rmeuth01/Astro/Software/FrontEnd/es-theme-epicnoir-ARES/_art/controllers/lightgun.png

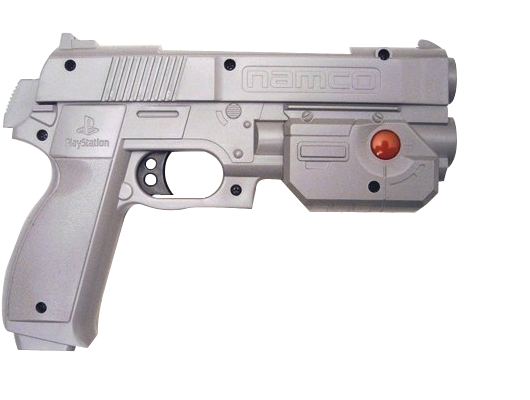
Software/FrontEnd/es-theme-epicnoir-ARES/_art/controllers/lightgun.png
