rmeuth01/Astro/Software/FrontEnd/es-theme-epicnoir-ARES/_art/controllers/3ds.png

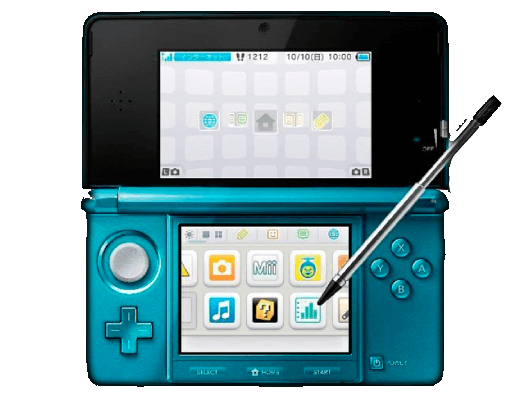
Software/FrontEnd/es-theme-epicnoir-ARES/_art/controllers/3ds.png
