rmeuth01/Astro/Software/FrontEnd/es-theme-epicnoir-ARES/_art/controllers/3do.png

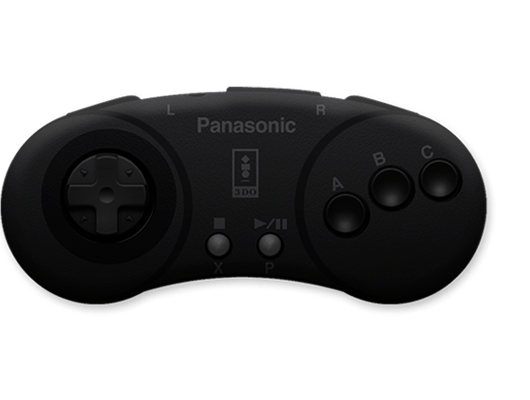
Software/FrontEnd/es-theme-epicnoir-ARES/_art/controllers/3do.png
