rmeuth01/Astro/Software/FrontEnd/es-theme-epicnoir-ARES/_art/controllers/action.png

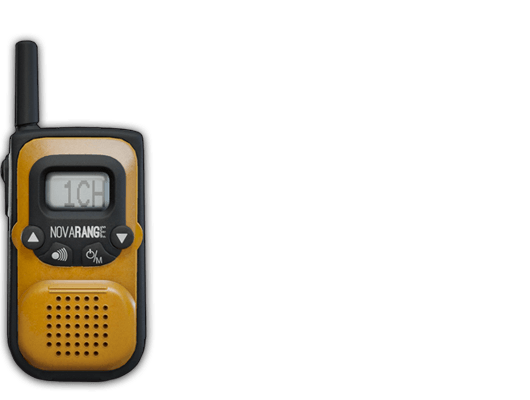
Software/FrontEnd/es-theme-epicnoir-ARES/_art/controllers/action.png
