rmeuth01/Astro/Software/FrontEnd/es-theme-epicnoir-ARES/_art/controllers/adventure.png

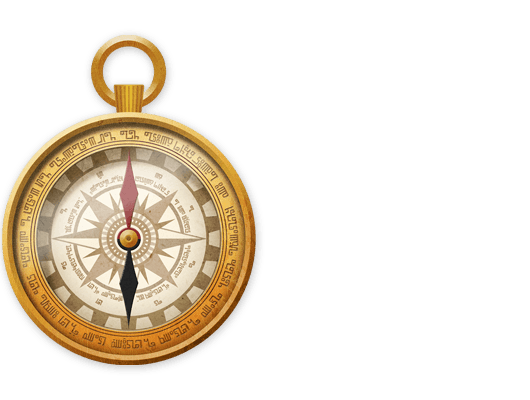
Software/FrontEnd/es-theme-epicnoir-ARES/_art/controllers/adventure.png
