rmeuth01/Astro/Software/FrontEnd/es-theme-epicnoir-ARES/_art/controllers/amiga1200.png

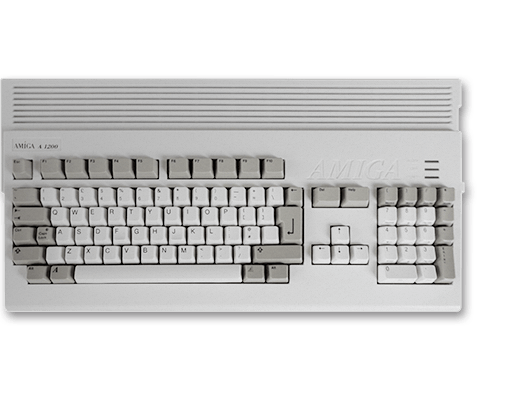
Software/FrontEnd/es-theme-epicnoir-ARES/_art/controllers/amiga1200.png
