rmeuth01/Astro/Software/FrontEnd/es-theme-epicnoir-ARES/_art/controllers/amstradcpc.png

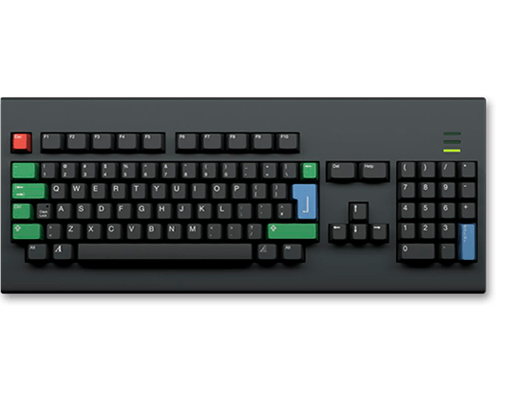
Software/FrontEnd/es-theme-epicnoir-ARES/_art/controllers/amstradcpc.png
