rmeuth01/Astro/Software/FrontEnd/es-theme-epicnoir-ARES/_art/controllers/arcade.png

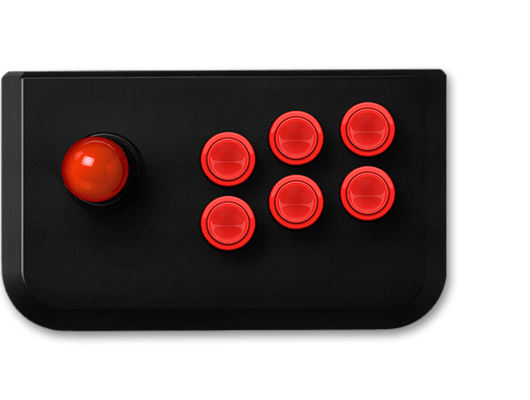
Software/FrontEnd/es-theme-epicnoir-ARES/_art/controllers/arcade.png
