rmeuth01/Astro/Software/FrontEnd/es-theme-epicnoir-ARES/_art/controllers/atari2600.png

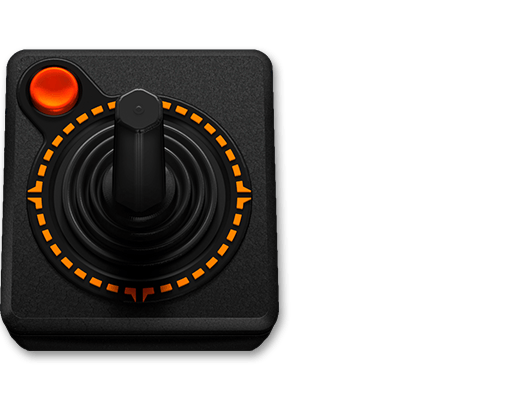
Software/FrontEnd/es-theme-epicnoir-ARES/_art/controllers/atari2600.png
