rmeuth01/Astro/Software/FrontEnd/es-theme-epicnoir-ARES/_art/controllers/atari5200.png

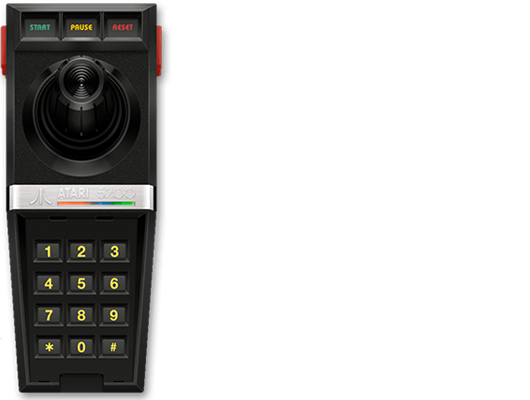
Software/FrontEnd/es-theme-epicnoir-ARES/_art/controllers/atari5200.png
