rmeuth01/Astro/Software/FrontEnd/es-theme-epicnoir-ARES/_art/controllers/atari7800.png

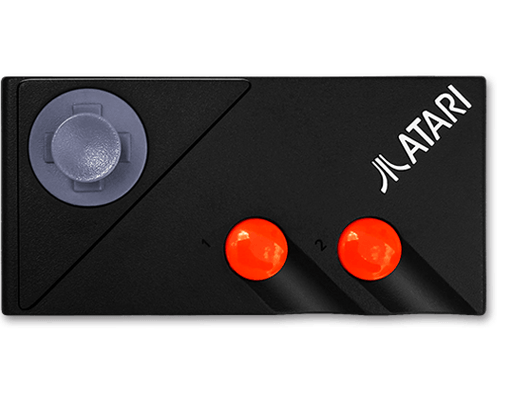
Software/FrontEnd/es-theme-epicnoir-ARES/_art/controllers/atari7800.png
