rmeuth01/Astro/Software/FrontEnd/es-theme-epicnoir-ARES/_art/controllers/atarijaguar.png

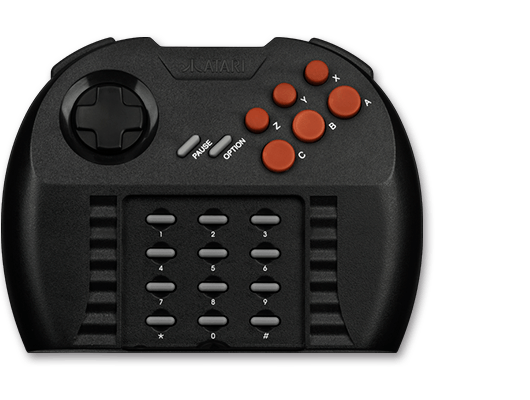
Software/FrontEnd/es-theme-epicnoir-ARES/_art/controllers/atarijaguar.png
