rmeuth01/Astro/Software/FrontEnd/es-theme-epicnoir-ARES/_art/controllers/atarilynx.png

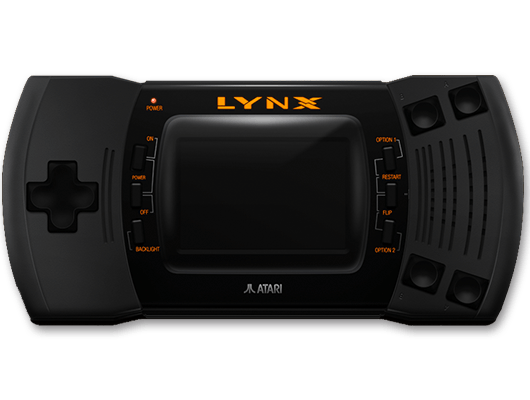
Software/FrontEnd/es-theme-epicnoir-ARES/_art/controllers/atarilynx.png
