rmeuth01/Astro/Software/FrontEnd/es-theme-epicnoir-ARES/_art/controllers/atarist.png

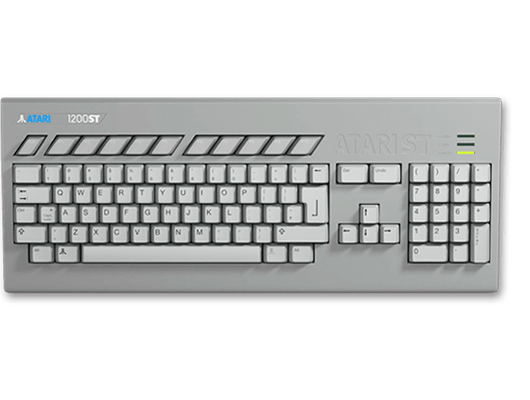
Software/FrontEnd/es-theme-epicnoir-ARES/_art/controllers/atarist.png
