rmeuth01/Astro/Software/FrontEnd/es-theme-epicnoir-ARES/_art/controllers/auto-allgames.png

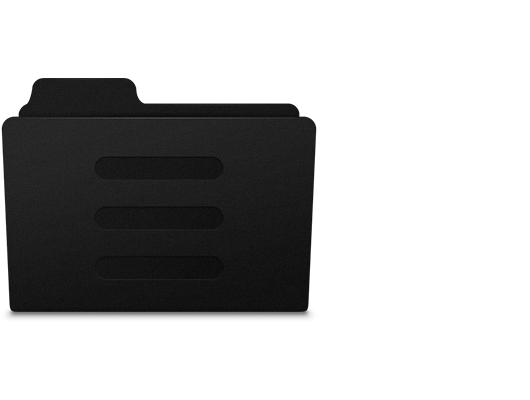
Software/FrontEnd/es-theme-epicnoir-ARES/_art/controllers/auto-allgames.png
