rmeuth01/Astro/Software/FrontEnd/es-theme-epicnoir-ARES/_art/controllers/btmups.png

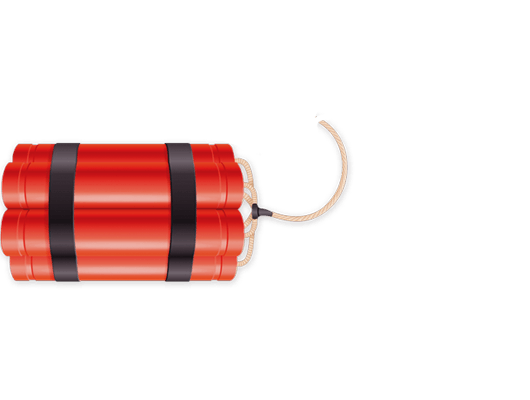
Software/FrontEnd/es-theme-epicnoir-ARES/_art/controllers/btmups.png
