rmeuth01/Astro/Software/FrontEnd/es-theme-epicnoir-ARES/_art/controllers/c16.png

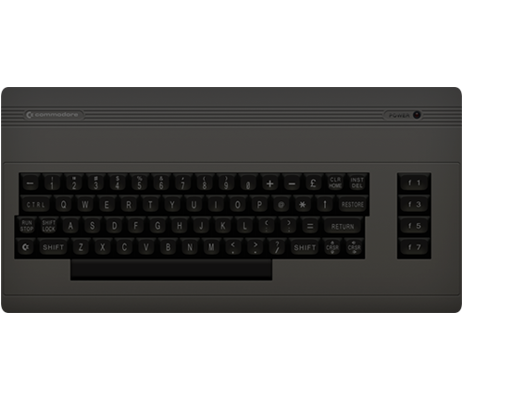
Software/FrontEnd/es-theme-epicnoir-ARES/_art/controllers/c16.png
