rmeuth01/Astro/Software/FrontEnd/es-theme-epicnoir-ARES/_art/controllers/coco.png

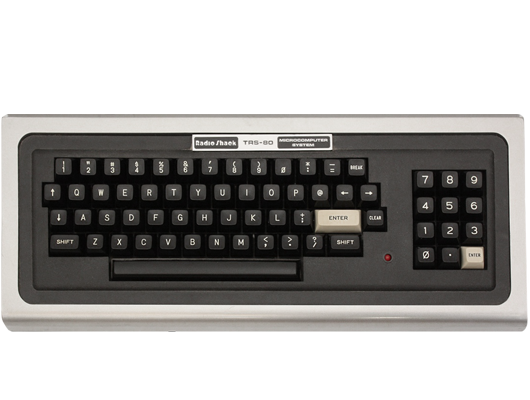
Software/FrontEnd/es-theme-epicnoir-ARES/_art/controllers/coco.png
