rmeuth01/Astro/Software/FrontEnd/es-theme-epicnoir-ARES/_art/controllers/colecovision.png

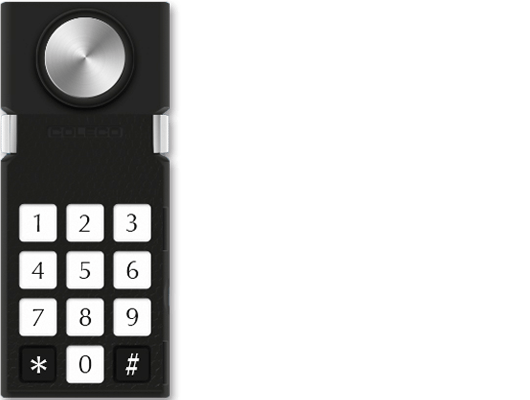
Software/FrontEnd/es-theme-epicnoir-ARES/_art/controllers/colecovision.png
