rmeuth01/Astro/Software/FrontEnd/es-theme-epicnoir-ARES/_art/controllers/dreamcast.png

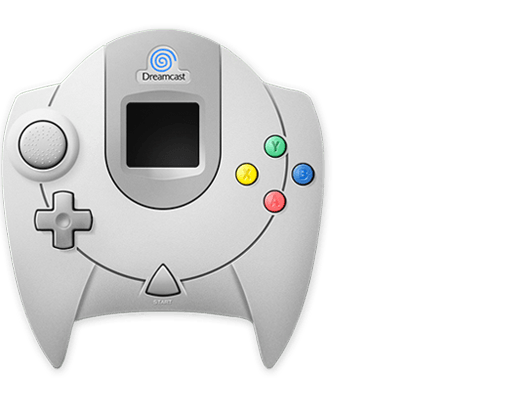
Software/FrontEnd/es-theme-epicnoir-ARES/_art/controllers/dreamcast.png
