rmeuth01/Astro/Software/FrontEnd/es-theme-epicnoir-ARES/_art/controllers/famicom.png

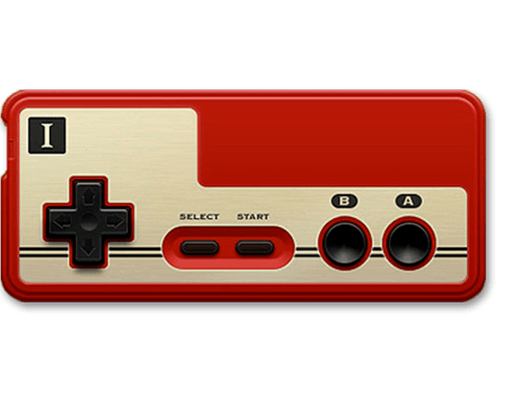
Software/FrontEnd/es-theme-epicnoir-ARES/_art/controllers/famicom.png
