rmeuth01/Astro/Software/FrontEnd/es-theme-epicnoir-ARES/_art/controllers/fighting.png

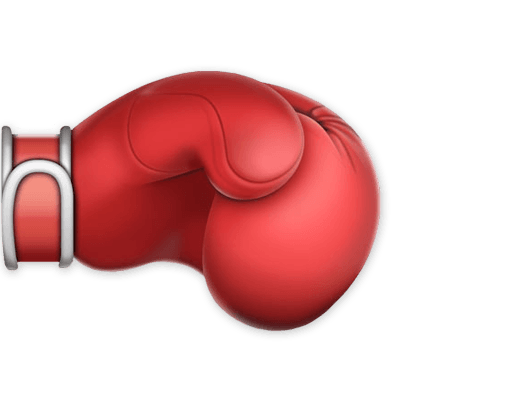
Software/FrontEnd/es-theme-epicnoir-ARES/_art/controllers/fighting.png
