rmeuth01/Astro/Software/FrontEnd/es-theme-epicnoir-ARES/_art/controllers/gameandwatch.png

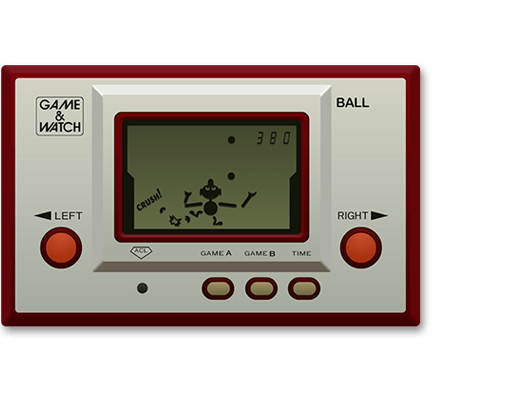
Software/FrontEnd/es-theme-epicnoir-ARES/_art/controllers/gameandwatch.png
