rmeuth01/Astro/Software/FrontEnd/es-theme-epicnoir-ARES/_art/controllers/gamegear.png

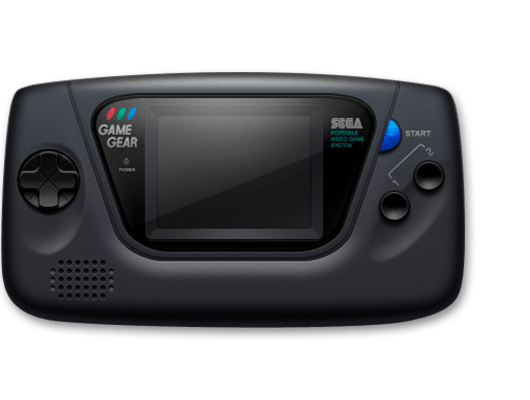
Software/FrontEnd/es-theme-epicnoir-ARES/_art/controllers/gamegear.png
