rmeuth01/Astro/Software/FrontEnd/es-theme-epicnoir-ARES/_art/controllers/gb.png

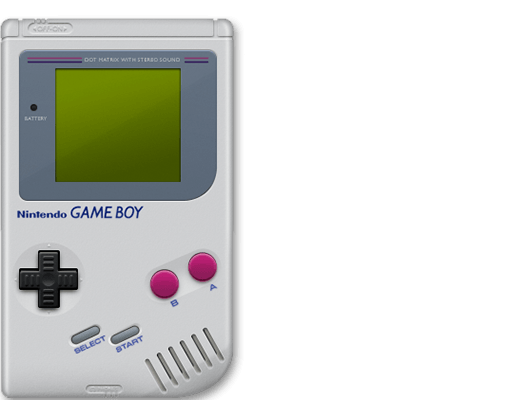
Software/FrontEnd/es-theme-epicnoir-ARES/_art/controllers/gb.png
