rmeuth01/Astro/Software/FrontEnd/es-theme-epicnoir-ARES/_art/controllers/gba.png

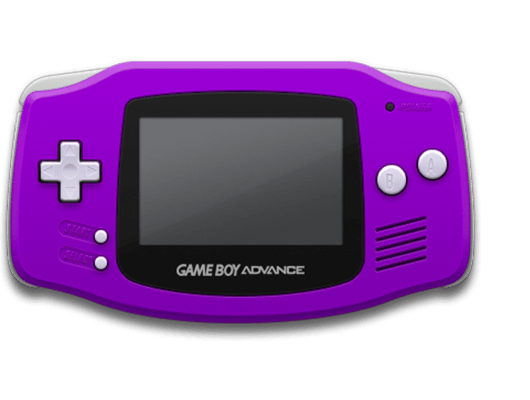
Software/FrontEnd/es-theme-epicnoir-ARES/_art/controllers/gba.png
