rmeuth01/Astro/Software/FrontEnd/es-theme-epicnoir-ARES/_art/controllers/gbc.png

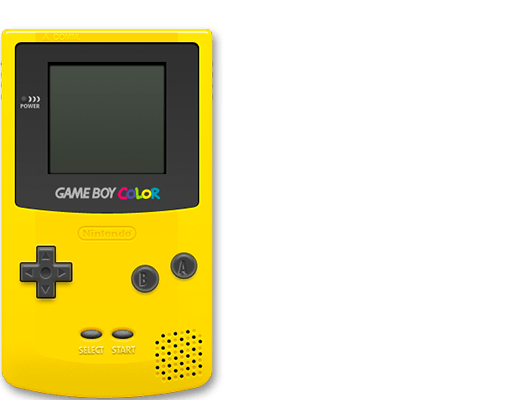
Software/FrontEnd/es-theme-epicnoir-ARES/_art/controllers/gbc.png
