rmeuth01/Astro/Software/FrontEnd/es-theme-epicnoir-ARES/_art/controllers/gc.png

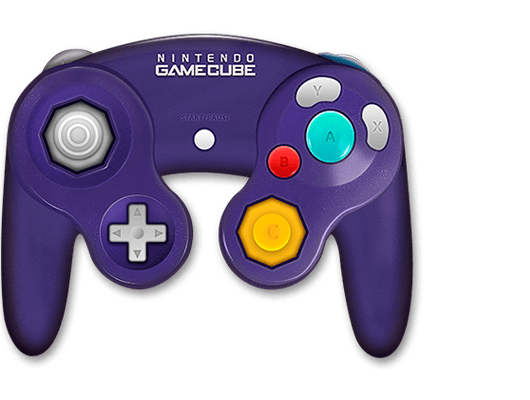
Software/FrontEnd/es-theme-epicnoir-ARES/_art/controllers/gc.png
