rmeuth01/Astro/Software/FrontEnd/es-theme-epicnoir-ARES/_art/controllers/genesis.png

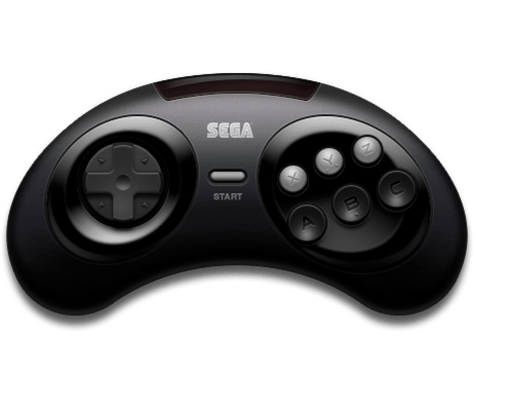
Software/FrontEnd/es-theme-epicnoir-ARES/_art/controllers/genesis.png
