rmeuth01/Astro/Software/FrontEnd/es-theme-epicnoir-ARES/_art/controllers/intellivision.png

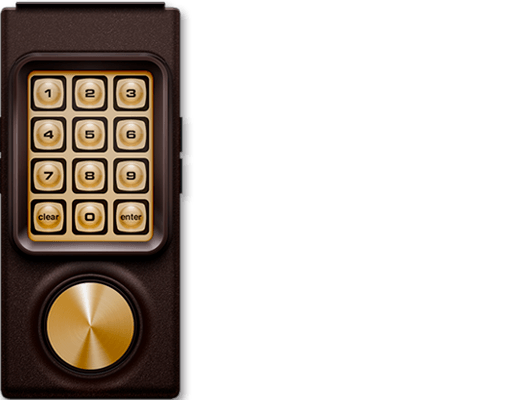
Software/FrontEnd/es-theme-epicnoir-ARES/_art/controllers/intellivision.png
