rmeuth01/Astro/Software/FrontEnd/es-theme-epicnoir-ARES/_art/controllers/kids.png

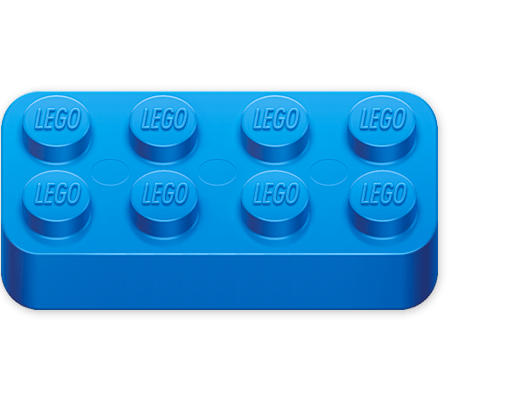
Software/FrontEnd/es-theme-epicnoir-ARES/_art/controllers/kids.png
