rmeuth01/Astro/Software/FrontEnd/es-theme-epicnoir-ARES/_art/controllers/kodi.png

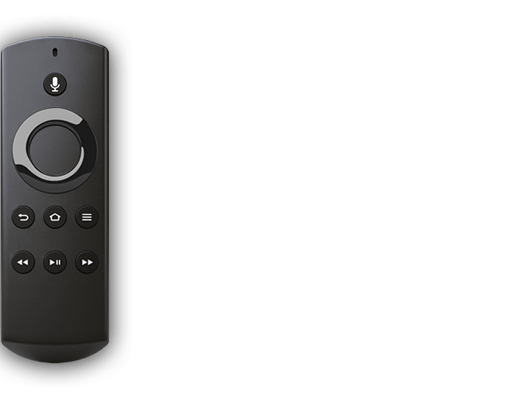
Software/FrontEnd/es-theme-epicnoir-ARES/_art/controllers/kodi.png
