rmeuth01/Astro/Software/FrontEnd/es-theme-epicnoir-ARES/_art/controllers/mastersystem.png

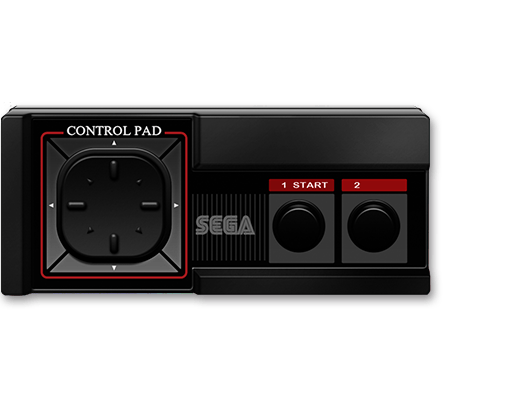
Software/FrontEnd/es-theme-epicnoir-ARES/_art/controllers/mastersystem.png
