rmeuth01/Astro/Software/FrontEnd/es-theme-epicnoir-ARES/_art/controllers/msx2.png

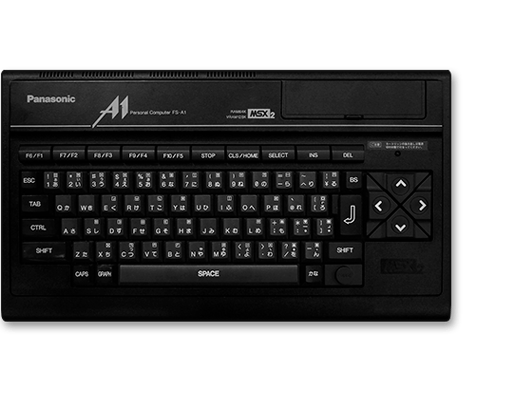
Software/FrontEnd/es-theme-epicnoir-ARES/_art/controllers/msx2.png
