rmeuth01/Astro/Software/FrontEnd/es-theme-epicnoir-ARES/_art/controllers/msx-fs8.png

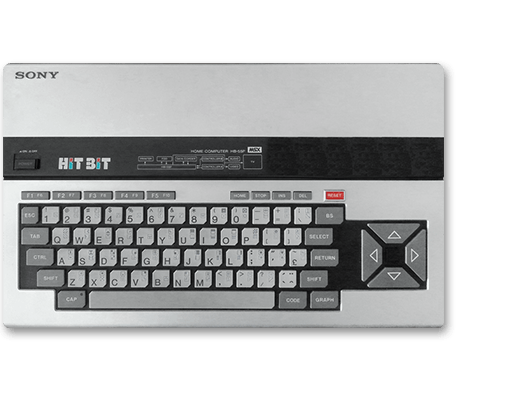
Software/FrontEnd/es-theme-epicnoir-ARES/_art/controllers/msx-fs8.png
