rmeuth01/Astro/Software/FrontEnd/es-theme-epicnoir-ARES/_art/controllers/n64.png

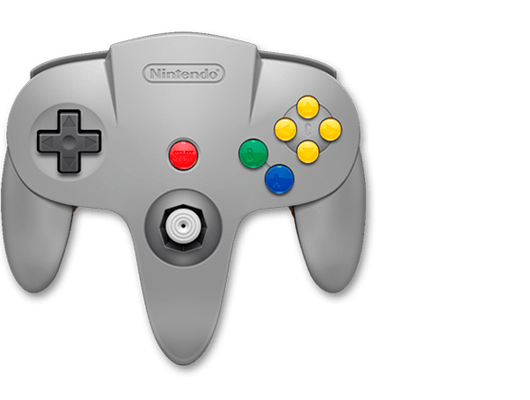
Software/FrontEnd/es-theme-epicnoir-ARES/_art/controllers/n64.png
