rmeuth01/Astro/Software/FrontEnd/es-theme-epicnoir-ARES/_art/controllers/nds.png

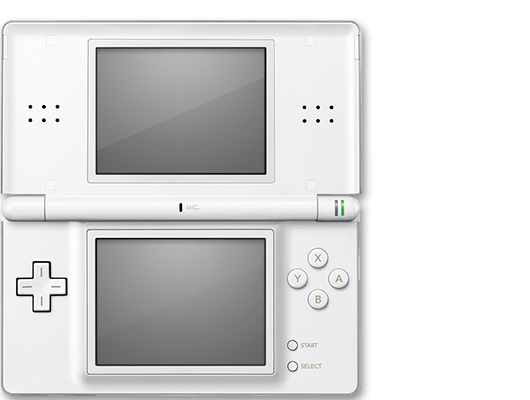
Software/FrontEnd/es-theme-epicnoir-ARES/_art/controllers/nds.png
