rmeuth01/Astro/Software/FrontEnd/es-theme-epicnoir-ARES/_art/controllers/neogeo.png

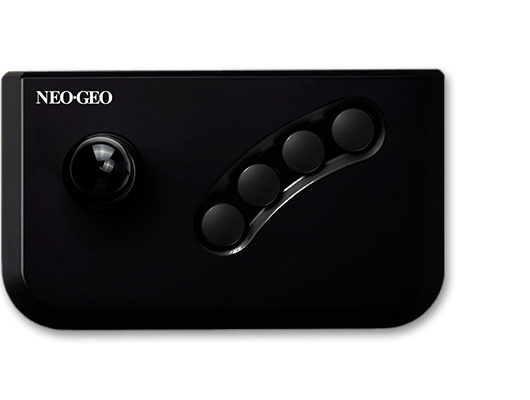
Software/FrontEnd/es-theme-epicnoir-ARES/_art/controllers/neogeo.png
