rmeuth01/Astro/Software/FrontEnd/es-theme-epicnoir-ARES/_art/controllers/neogeocd.png

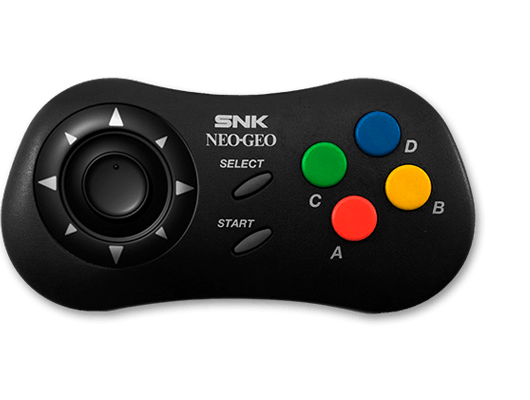
Software/FrontEnd/es-theme-epicnoir-ARES/_art/controllers/neogeocd.png
