rmeuth01/Astro/Software/FrontEnd/es-theme-epicnoir-ARES/_art/controllers/nes.png

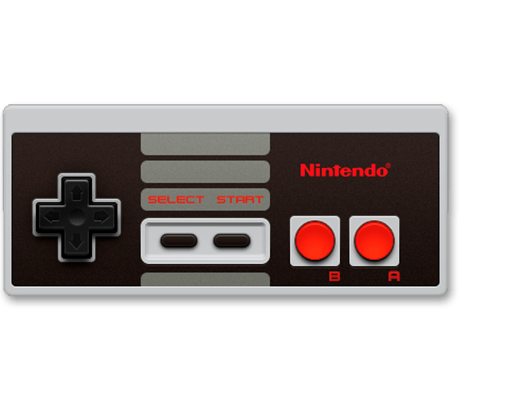
Software/FrontEnd/es-theme-epicnoir-ARES/_art/controllers/nes.png
