rmeuth01/Astro/Software/FrontEnd/es-theme-epicnoir-ARES/_art/controllers/ngp.png

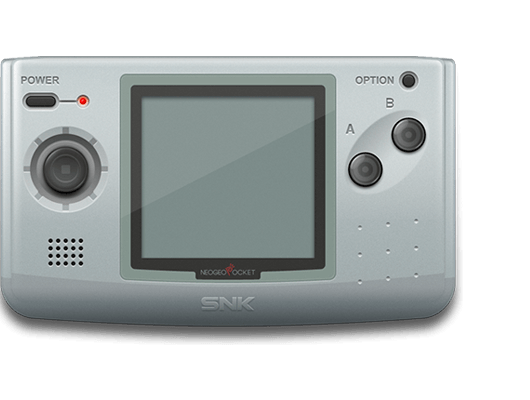
Software/FrontEnd/es-theme-epicnoir-ARES/_art/controllers/ngp.png
