rmeuth01/Astro/Software/FrontEnd/es-theme-epicnoir-ARES/_art/controllers/pc98.png

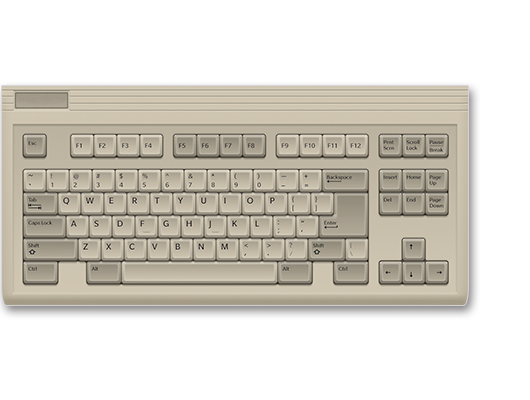
Software/FrontEnd/es-theme-epicnoir-ARES/_art/controllers/pc98.png
