rmeuth01/Astro/Software/FrontEnd/es-theme-epicnoir-ARES/_art/controllers/pce-cd.png

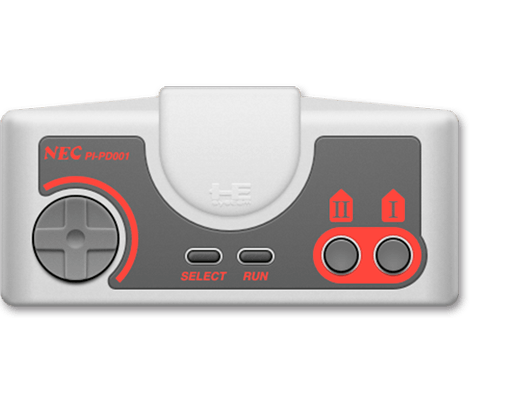
Software/FrontEnd/es-theme-epicnoir-ARES/_art/controllers/pce-cd.png
