rmeuth01/Astro/Software/FrontEnd/es-theme-epicnoir-ARES/_art/controllers/platformers.png

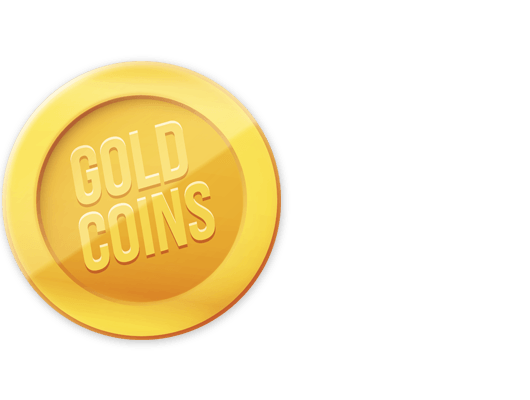
Software/FrontEnd/es-theme-epicnoir-ARES/_art/controllers/platformers.png
