rmeuth01/Astro/Software/FrontEnd/es-theme-epicnoir-ARES/_art/controllers/ports.png

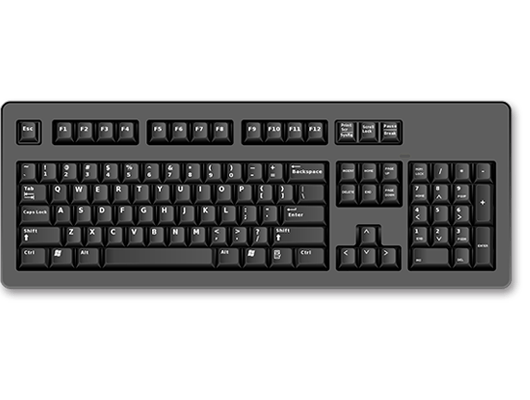
Software/FrontEnd/es-theme-epicnoir-ARES/_art/controllers/ports.png
