rmeuth01/Astro/Software/FrontEnd/es-theme-epicnoir-ARES/_art/controllers/power.png

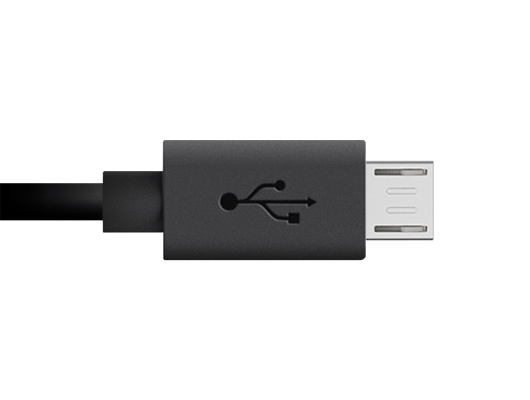
Software/FrontEnd/es-theme-epicnoir-ARES/_art/controllers/power.png
