rmeuth01/Astro/Software/FrontEnd/es-theme-epicnoir-ARES/_art/controllers/ps2.png

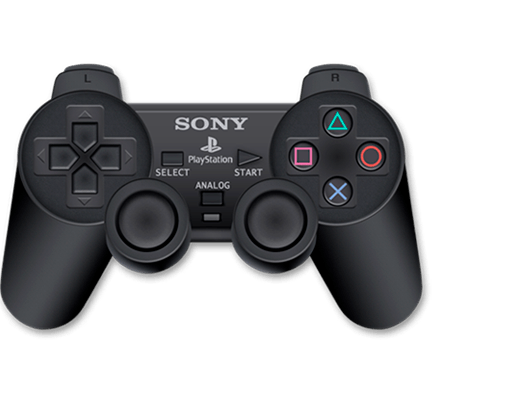
Software/FrontEnd/es-theme-epicnoir-ARES/_art/controllers/ps2.png
