rmeuth01/Astro/Software/FrontEnd/es-theme-epicnoir-ARES/_art/controllers/ps3.png

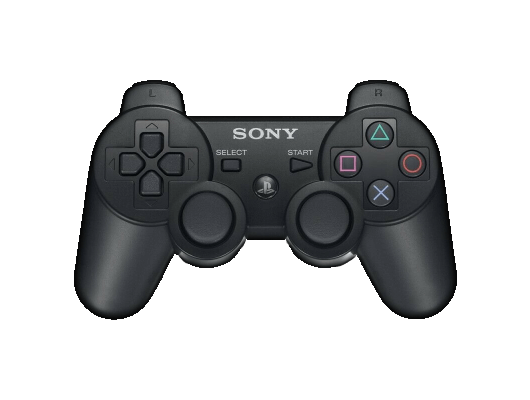
Software/FrontEnd/es-theme-epicnoir-ARES/_art/controllers/ps3.png
