rmeuth01/Astro/Software/FrontEnd/es-theme-epicnoir-ARES/_art/controllers/psp.png

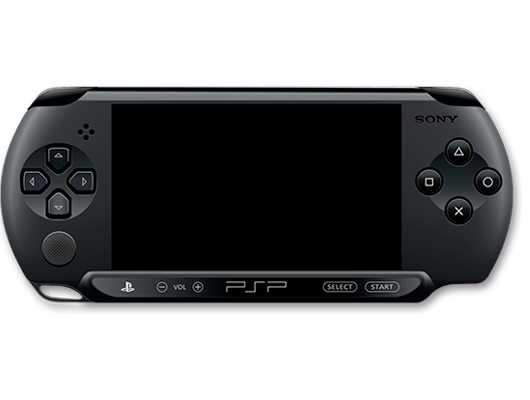
Software/FrontEnd/es-theme-epicnoir-ARES/_art/controllers/psp.png
