rmeuth01/Astro/Software/FrontEnd/es-theme-epicnoir-ARES/_art/controllers/psx.png

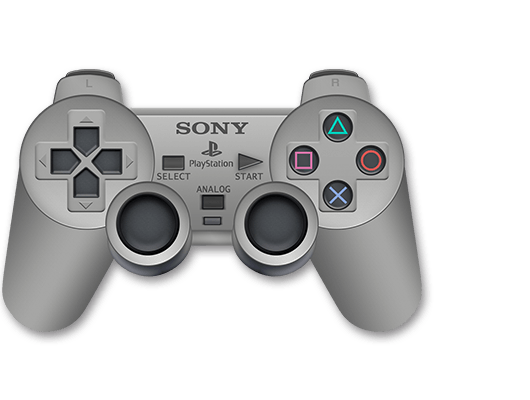
Software/FrontEnd/es-theme-epicnoir-ARES/_art/controllers/psx.png
