rmeuth01/Astro/Software/FrontEnd/es-theme-epicnoir-ARES/_art/controllers/puzzle.png

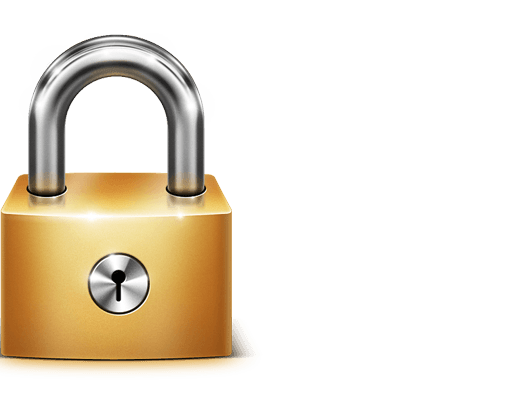
Software/FrontEnd/es-theme-epicnoir-ARES/_art/controllers/puzzle.png
