rmeuth01/Astro/Software/FrontEnd/es-theme-epicnoir-ARES/_art/controllers/racing.png

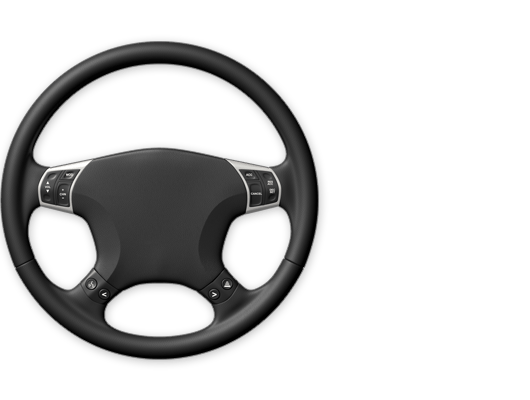
Software/FrontEnd/es-theme-epicnoir-ARES/_art/controllers/racing.png
