rmeuth01/Astro/Software/FrontEnd/es-theme-epicnoir-ARES/_art/controllers/residualvm.png

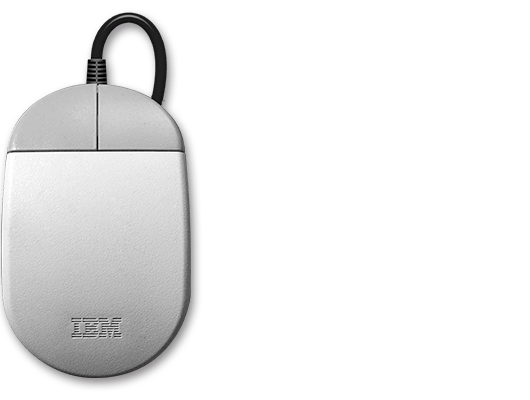
Software/FrontEnd/es-theme-epicnoir-ARES/_art/controllers/residualvm.png
