rmeuth01/Astro/Software/FrontEnd/es-theme-epicnoir-ARES/_art/controllers/retroarena.png

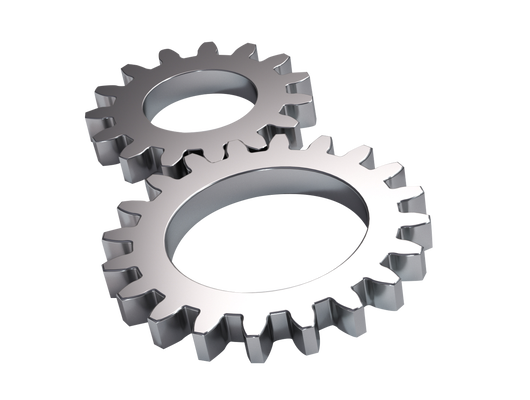
Software/FrontEnd/es-theme-epicnoir-ARES/_art/controllers/retroarena.png
