rmeuth01/Astro/Software/FrontEnd/es-theme-epicnoir-ARES/_art/controllers/retropie.png

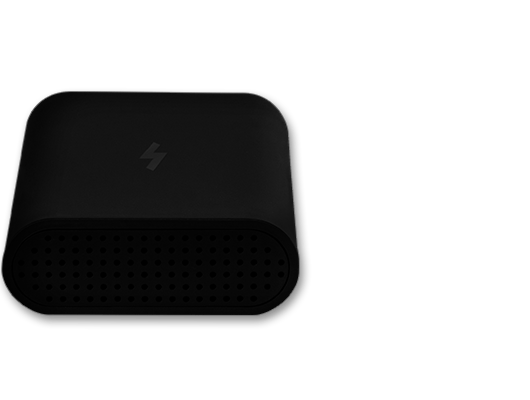
Software/FrontEnd/es-theme-epicnoir-ARES/_art/controllers/retropie.png
