rmeuth01/Astro/Software/FrontEnd/es-theme-epicnoir-ARES/_art/controllers/saturn.png

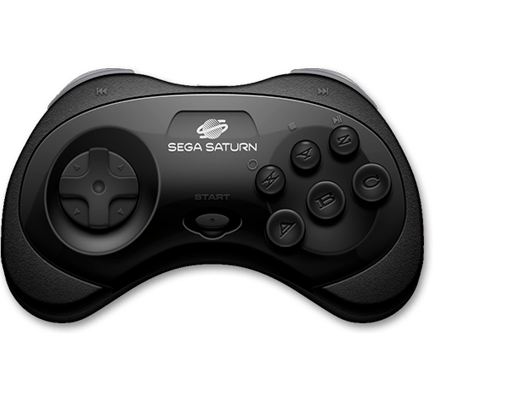
Software/FrontEnd/es-theme-epicnoir-ARES/_art/controllers/saturn.png
