rmeuth01/Astro/Software/FrontEnd/es-theme-epicnoir-ARES/_art/controllers/sfc.png

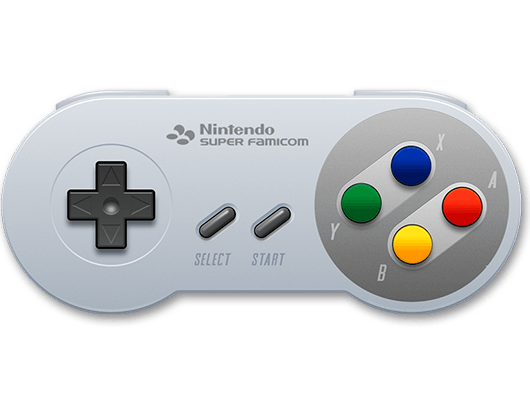
Software/FrontEnd/es-theme-epicnoir-ARES/_art/controllers/sfc.png
