rmeuth01/Astro/Software/FrontEnd/es-theme-epicnoir-ARES/_art/controllers/shmups.png

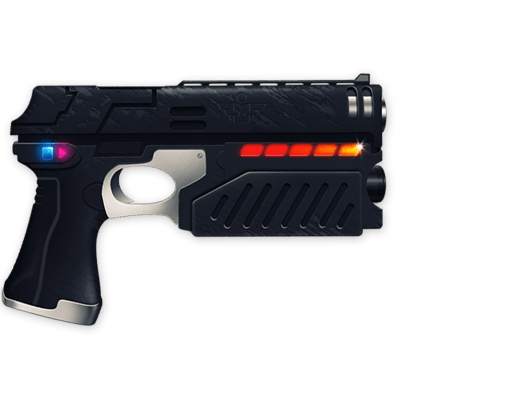
Software/FrontEnd/es-theme-epicnoir-ARES/_art/controllers/shmups.png
