rmeuth01/Astro/Software/FrontEnd/es-theme-epicnoir-ARES/_art/controllers/sports.png

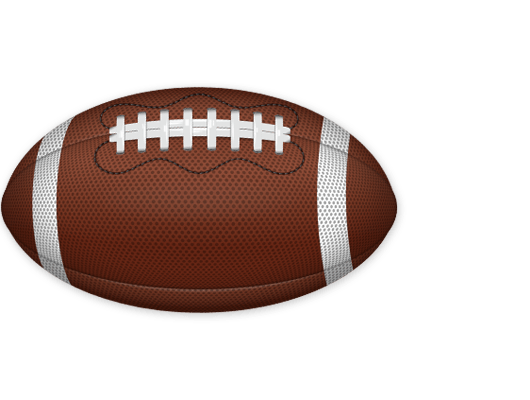
Software/FrontEnd/es-theme-epicnoir-ARES/_art/controllers/sports.png
