rmeuth01/Astro/Software/FrontEnd/es-theme-epicnoir-ARES/_art/controllers/steam.png

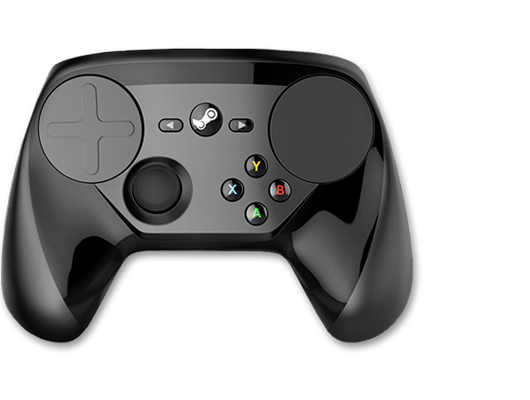
Software/FrontEnd/es-theme-epicnoir-ARES/_art/controllers/steam.png
