rmeuth01/Astro/Software/FrontEnd/es-theme-epicnoir-ARES/_art/controllers/strategy.png

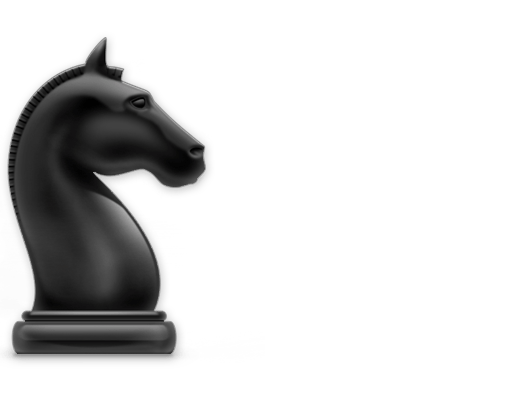
Software/FrontEnd/es-theme-epicnoir-ARES/_art/controllers/strategy.png
