rmeuth01/Astro/Software/FrontEnd/es-theme-epicnoir-ARES/_art/controllers/supergrafx.png

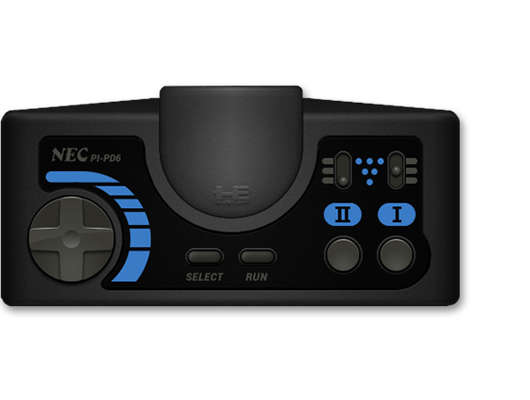
Software/FrontEnd/es-theme-epicnoir-ARES/_art/controllers/supergrafx.png
