rmeuth01/Astro/Software/FrontEnd/es-theme-epicnoir-ARES/_art/controllers/switch.png

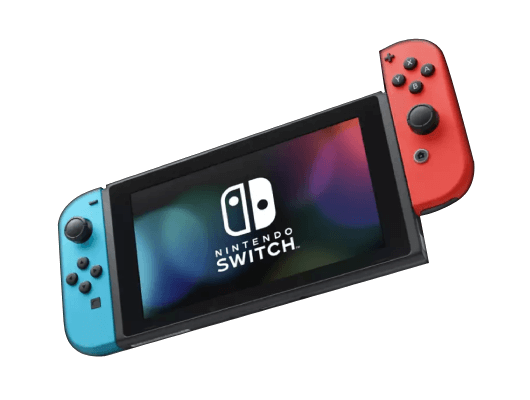
Software/FrontEnd/es-theme-epicnoir-ARES/_art/controllers/switch.png
