rmeuth01/Astro/Software/FrontEnd/es-theme-epicnoir-ARES/_art/controllers/tg16.png

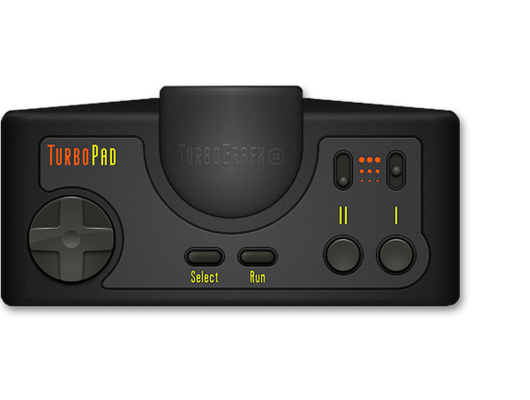
Software/FrontEnd/es-theme-epicnoir-ARES/_art/controllers/tg16.png
