rmeuth01/Astro/Software/FrontEnd/es-theme-epicnoir-ARES/_art/controllers/vectrex.png

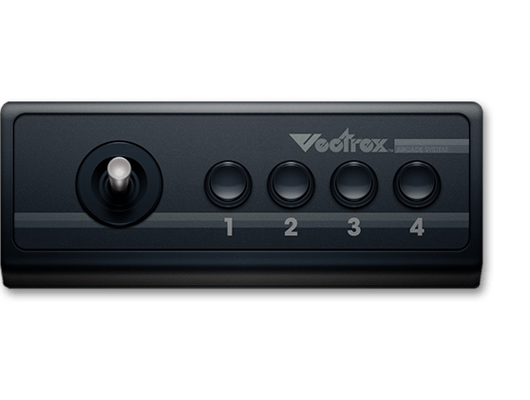
Software/FrontEnd/es-theme-epicnoir-ARES/_art/controllers/vectrex.png
