rmeuth01/Astro/Software/FrontEnd/es-theme-epicnoir-ARES/_art/controllers/virtualboy.png

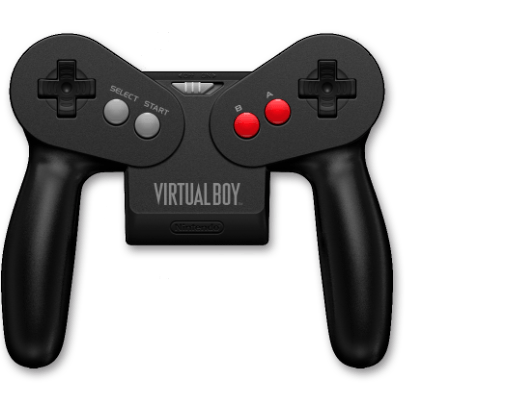
Software/FrontEnd/es-theme-epicnoir-ARES/_art/controllers/virtualboy.png
