rmeuth01/Astro/Software/FrontEnd/es-theme-epicnoir-ARES/_art/controllers/wii.png

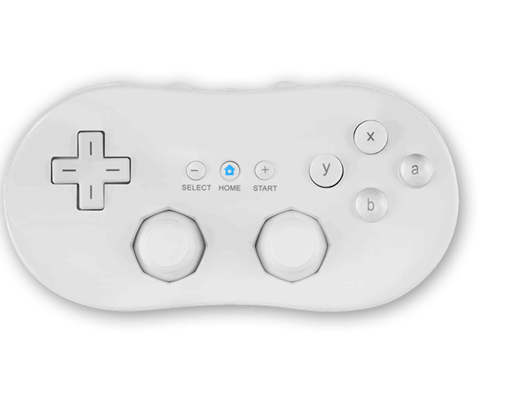
Software/FrontEnd/es-theme-epicnoir-ARES/_art/controllers/wii.png
