rmeuth01/Astro/Software/FrontEnd/es-theme-epicnoir-ARES/_art/controllers/wonderswan.png

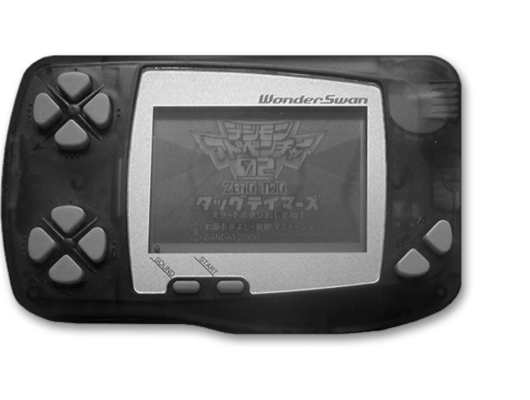
Software/FrontEnd/es-theme-epicnoir-ARES/_art/controllers/wonderswan.png
