rmeuth01/Astro/Software/FrontEnd/es-theme-epicnoir-ARES/_art/controllers/wonderswancolor.png

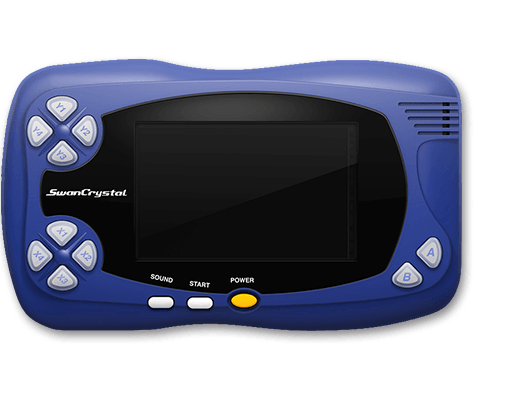
Software/FrontEnd/es-theme-epicnoir-ARES/_art/controllers/wonderswancolor.png
