rmeuth01/Astro/Software/FrontEnd/es-theme-epicnoir-ARES/_art/controllers/x68000.png

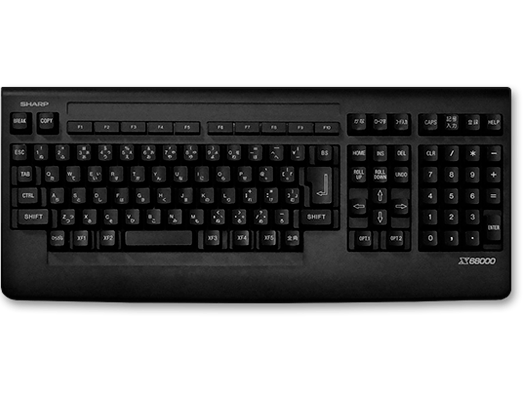
Software/FrontEnd/es-theme-epicnoir-ARES/_art/controllers/x68000.png
