rmeuth01/Astro/Software/FrontEnd/es-theme-epicnoir-ARES/_art/controllers/xbox360.png

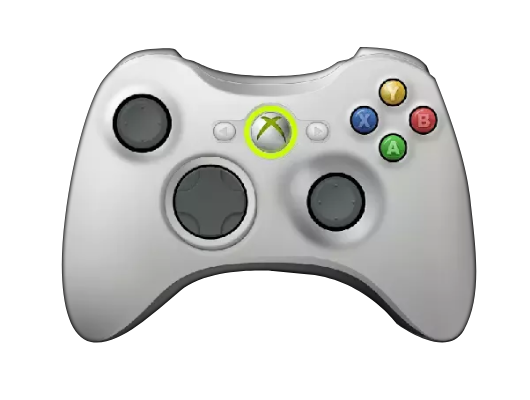
Software/FrontEnd/es-theme-epicnoir-ARES/_art/controllers/xbox360.png
