rmeuth01/Astro/Software/FrontEnd/es-theme-epicnoir-ARES/_art/controllers/xbox.png

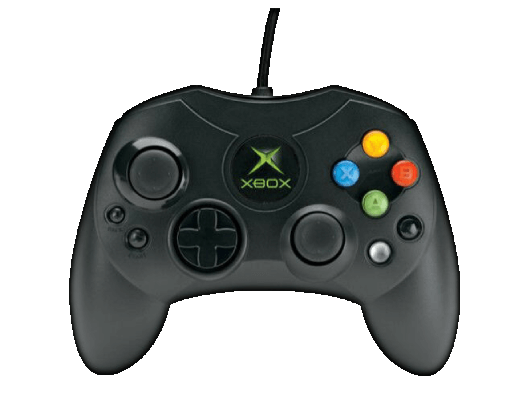
Software/FrontEnd/es-theme-epicnoir-ARES/_art/controllers/xbox.png
