rmeuth01/Astro/Software/FrontEnd/es-theme-epicnoir-ARES/_art/controllers/zx81.png

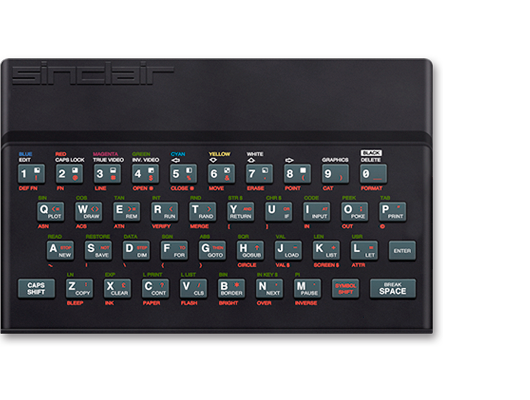
Software/FrontEnd/es-theme-epicnoir-ARES/_art/controllers/zx81.png
