rmeuth01/Astro/Software/FrontEnd/es-theme-epicnoir-ARES/_art/ingame-global-bg.jpg

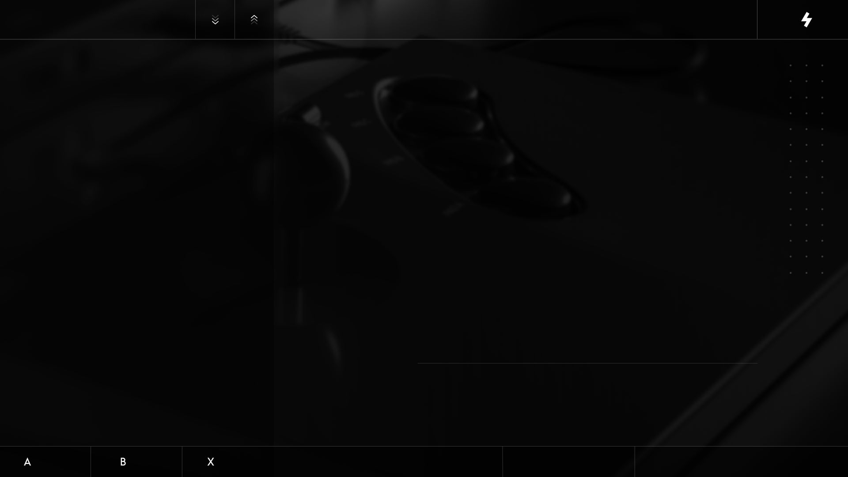
Software/FrontEnd/es-theme-epicnoir-ARES/_art/ingame-global-bg.jpg
