rmeuth01/Astro/Software/FrontEnd/es-theme-epicnoir-ARES/_art/samples/001.jpg

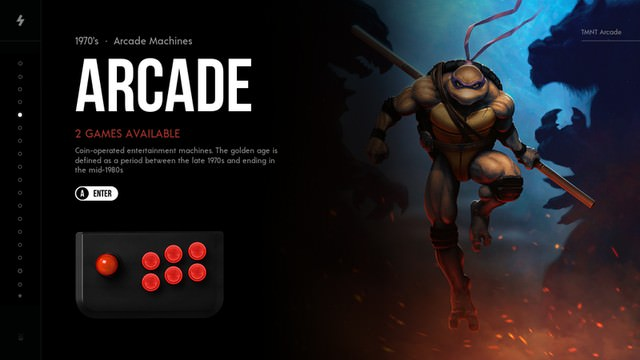
Software/FrontEnd/es-theme-epicnoir-ARES/_art/samples/001.jpg
