rmeuth01/Astro/Software/FrontEnd/es-theme-epicnoir-ARES/_art/samples/003.jpg

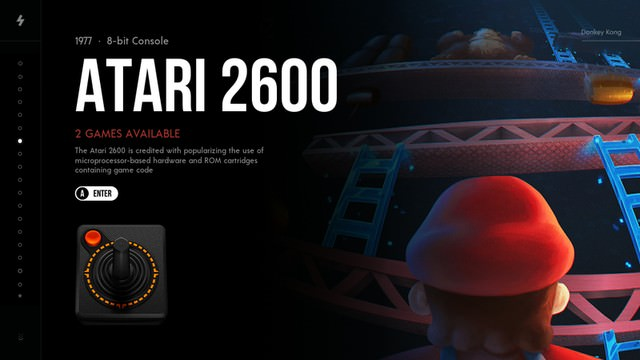
Software/FrontEnd/es-theme-epicnoir-ARES/_art/samples/003.jpg
