rmeuth01/Astro/Software/FrontEnd/es-theme-epicnoir-ARES/_art/samples/007.jpg

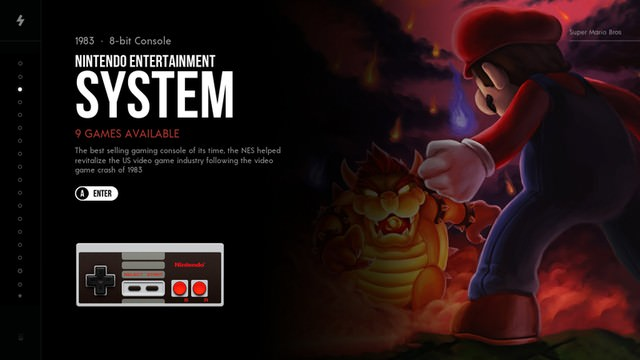
Software/FrontEnd/es-theme-epicnoir-ARES/_art/samples/007.jpg
