rmeuth01/Astro/Software/FrontEnd/es-theme-epicnoir-ARES/_art/samples/009.jpg

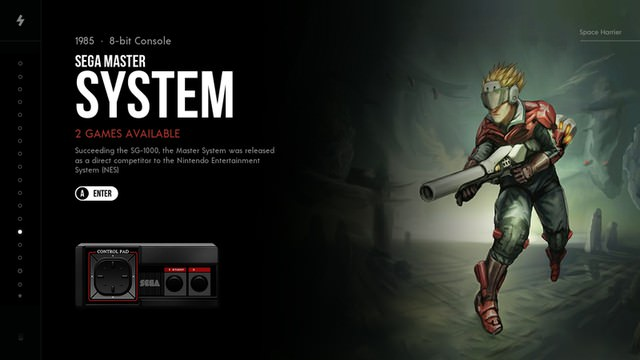
Software/FrontEnd/es-theme-epicnoir-ARES/_art/samples/009.jpg
