rmeuth01/Astro/Software/FrontEnd/power.png

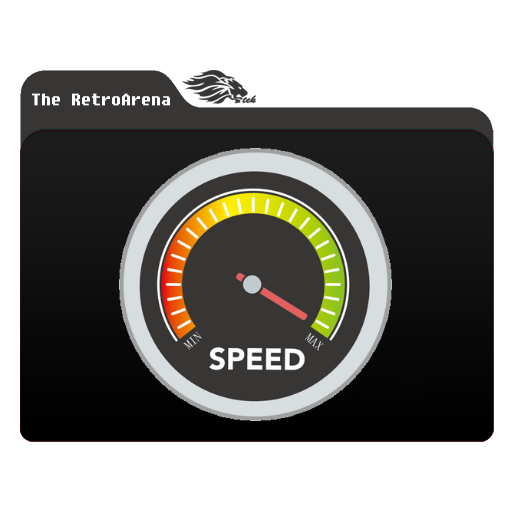
Software/FrontEnd/power.png
